kushima8/Re/Re64/Plate/re64r_top.dxf

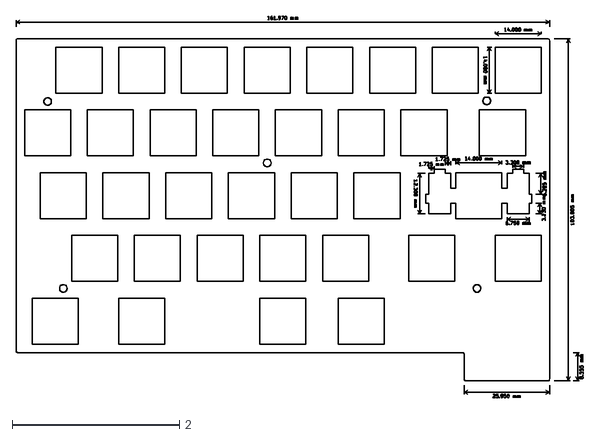
[picture p15: CAD file, 2020-08-09]
Re64/Plate/re64r_top.dxf
6.78 x 4.56
