kushima8/Re/Re93/Plate/re93r_bottom.dxf

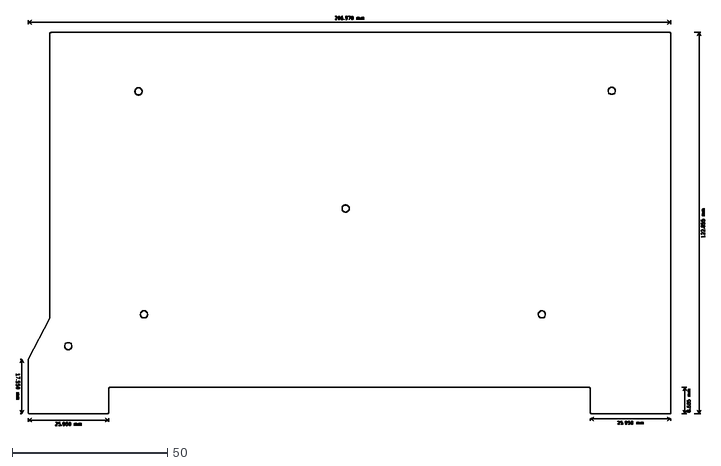
[picture p16: CAD file, 2021-01-07]
Re93/Plate/re93r_bottom.dxf
221.5 x 131.7
